zzeneg/molekula/pcbs/side36-minY/side36-right-mx-chocV2.step

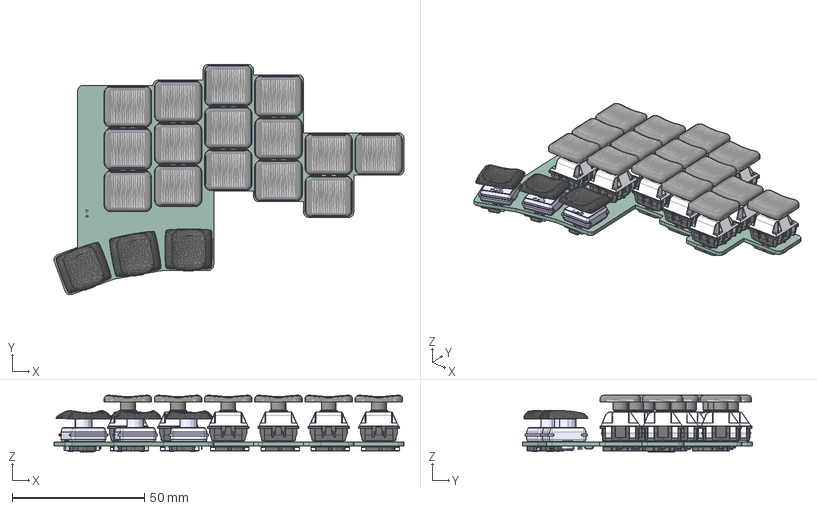
[picture p35: CAD file, 2025-01-04]
pcbs/side36-minY/side36-right-mx-chocV2.step
132.5 x 87.2 x 21.4 mm
SW_Cherry_MX_PCB_cp x 15
SW_Hotswap_Kailh_cp x 15
(Unsaved) x 15
keycap-mx-des-miny-minz-r3 v2 x 3
Kailh_PG1352 x 3
PG1350 x 3
D_SOD-123 Soldered v6 x 18
FPC-12
_autosave-pcb-right_PCB
