zzeneg/molekula/pcbs/tws-xiao-encoder/tws-xiao-encoder.step

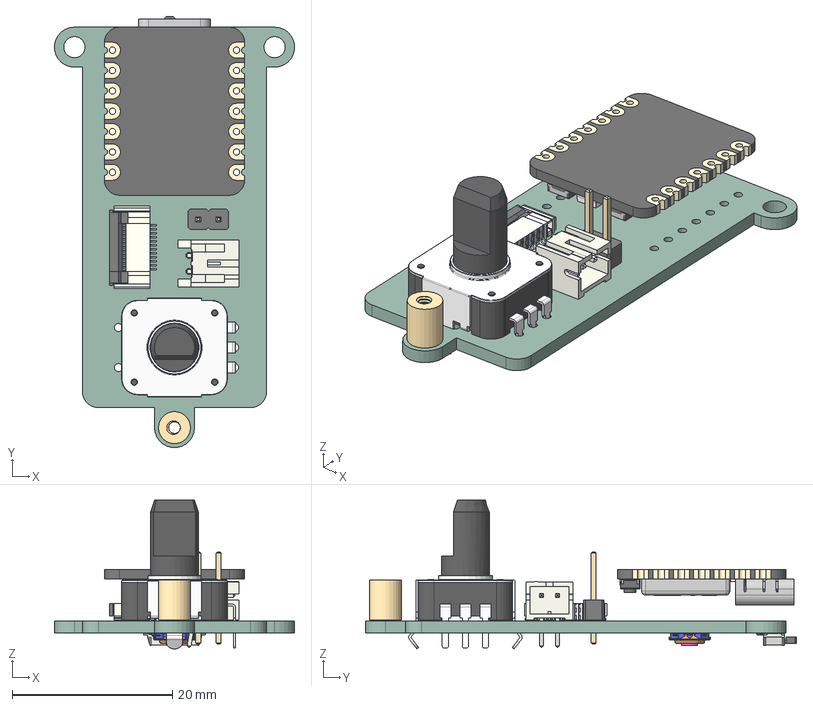
[picture p36: CAD file, 2026-09-22]
pcbs/tws-xiao-encoder/tws-xiao-encoder.step
30.0 x 53.8 x 18.6 mm
solder-nut v2
PinHeader_1x02_P254mm_Vertical
JST_S2B_PH_K
FPC-12
EC12_10mm (3)
Fusion_sp
Button_SW_SPST_SKQG_WithoutStem v1
type-c v2
smd_button v3
DOUT
DIN
VSS
VDD
smd_button v3(Mirror)
tws-xiao-encoder_PCB
