zzeneg/molekula/keyboards/Molekula2/case/bottom-right-mx cutout.dxf

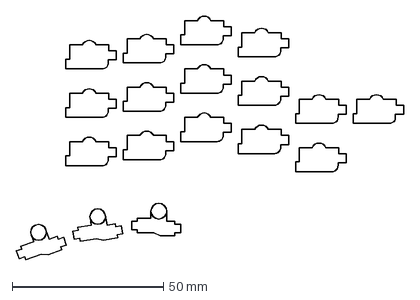
[picture p37: CAD file, 2026-05-30]
keyboards/Molekula2/case/bottom-right-mx cutout.dxf
128.1 x 80.6 mm
