zzeneg/molekula/keyboards/Molekula3/case/LP/center-nice-view.stl

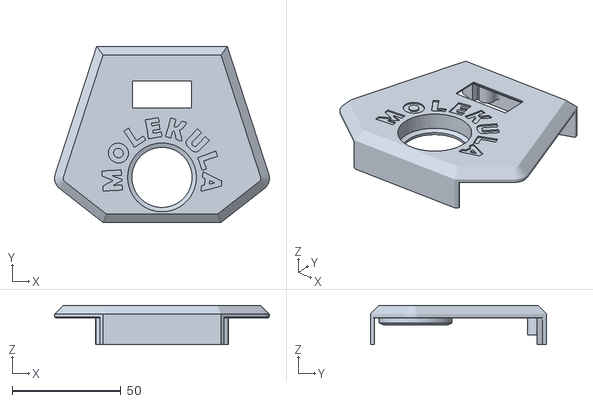
[picture p38: CAD file, 2026-05-30]
keyboards/Molekula3/case/LP/center-nice-view.stl
98.7 x 80.9 x 18.0
