zzeneg/molekula/keyboards/Molekula3/case/MX/top-left.stl

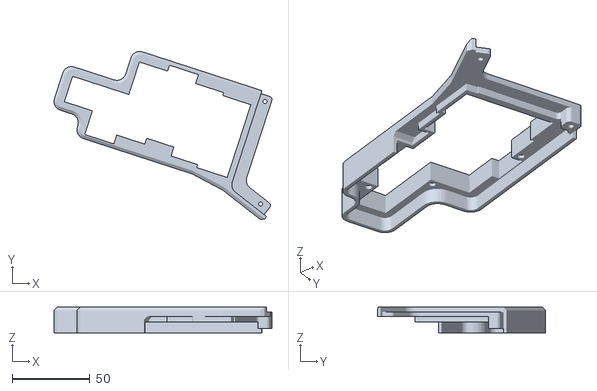
[picture p39: CAD file, 2026-05-30]
keyboards/Molekula3/case/MX/top-left.stl
140.1 x 108.1 x 16.5
