zzeneg/molekula/keyboards/MolekulaTWS/case/choc-spacing/tws.3mf

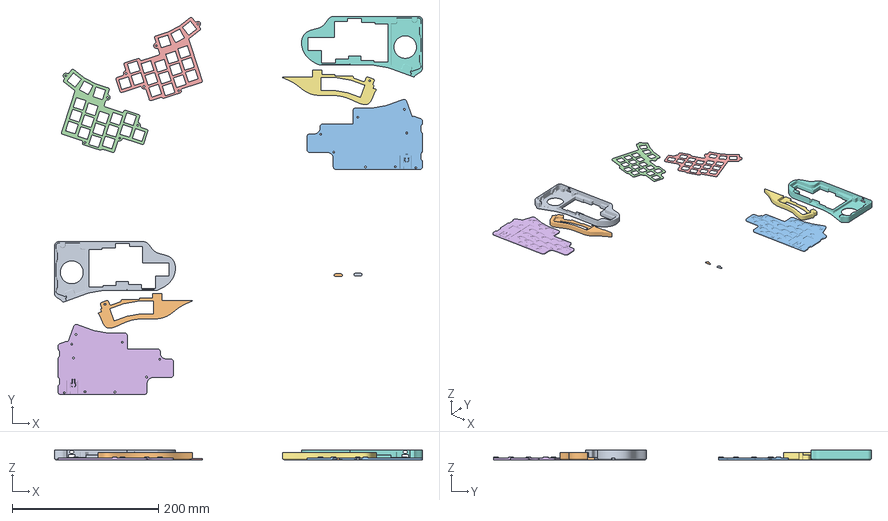
[picture p40: CAD file, 2026-09-22]
keyboards/MolekulaTWS/case/choc-spacing/tws.3mf
503.1 x 517.4 x 13.6 mm
tws-top-curved-left.stl
tws-thumb-curved-left.stl
tws-bottom-right.stl
plate-right.stl
plate-left.stl
tws-bottom-left.stl
tws-right-thumb.stl
tws-right-top.stl
tws-power-switch.stl x 2
