zzeneg/molekula/keyboards/MolekulaTWS/case/common/knob-lp.stl

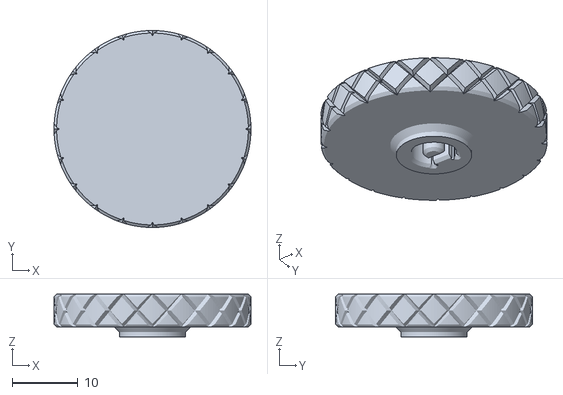
[picture p41: CAD file, 2026-09-22]
keyboards/MolekulaTWS/case/common/knob-lp.stl
30.0 x 30.0 x 6.50
