zzeneg/molekula/keycaps/MX-DES-minY/DES_r3_1.00u_x6.stl

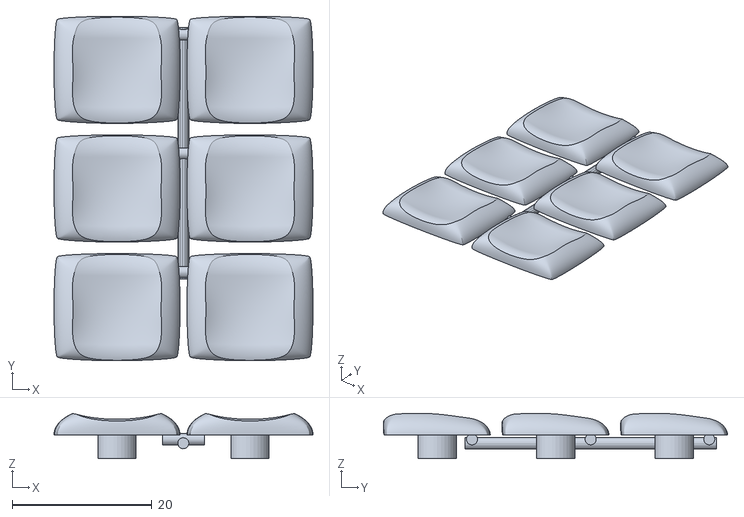
[picture p43: CAD file, 2025-01-04]
keycaps/MX-DES-minY/DES_r3_1.00u_x6.stl
37.1 x 49.4 x 6.47
