zzeneg/molekula/pcbs/central-promicro-encoder/connector-right.step

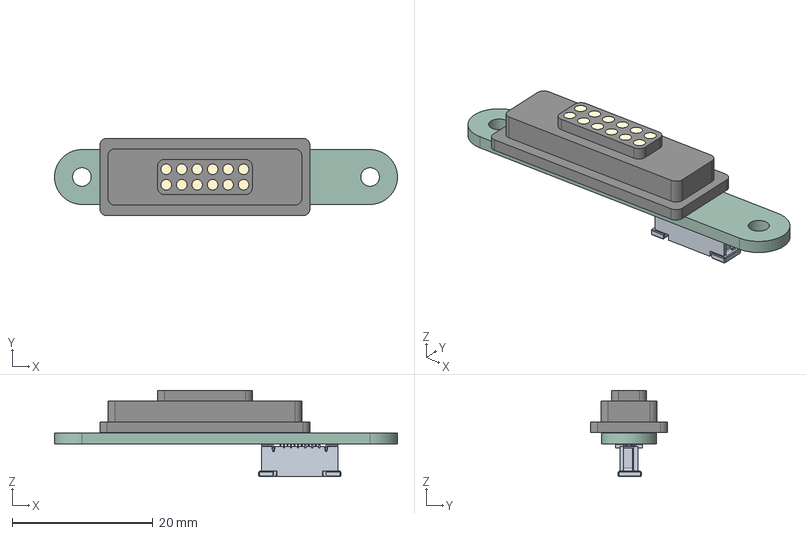
[picture p44: CAD file, 2024-11-01]
pcbs/central-promicro-encoder/connector-right.step
48.8 x 11.0 x 12.3 mm
Magnetic connector 12pin v2
C-1-1734742-2
connector-right_PCB
