zzeneg/molekula/keyboards/Molekula2/case/bottom-left-mx cutout.dxf

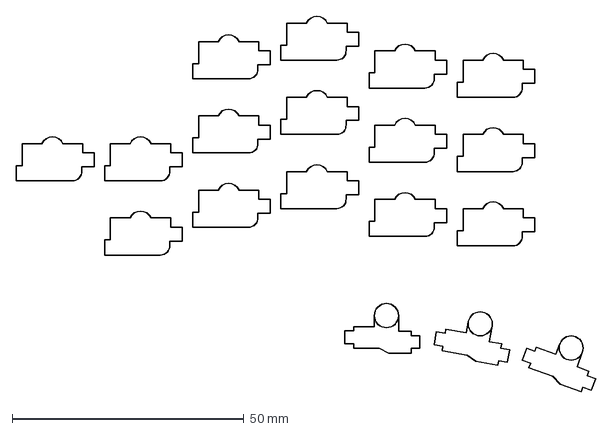
[picture p46: CAD file, 2026-05-30]
keyboards/Molekula2/case/bottom-left-mx cutout.dxf
124.8 x 80.9 mm
