zzeneg/molekula/keyboards/MolekulaTWS/case/choc-spacing/tws-bottom-left.stl

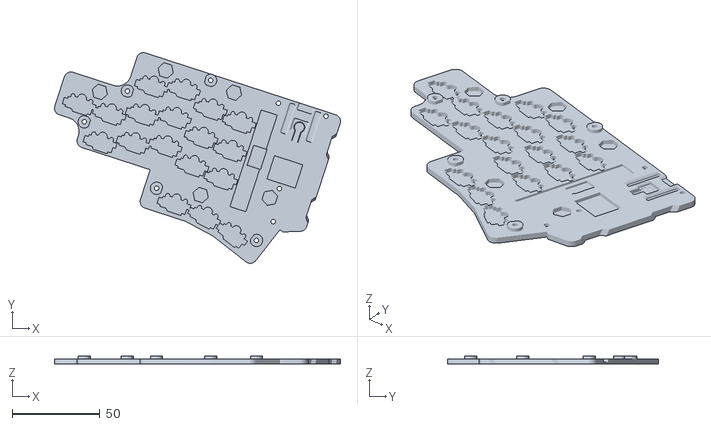
[picture p47: CAD file, 2026-09-22]
keyboards/MolekulaTWS/case/choc-spacing/tws-bottom-left.stl
163.4 x 120.3 x 4.40
