zzeneg/molekula/keyboards/MolekulaTWS/case/common/knob.stl

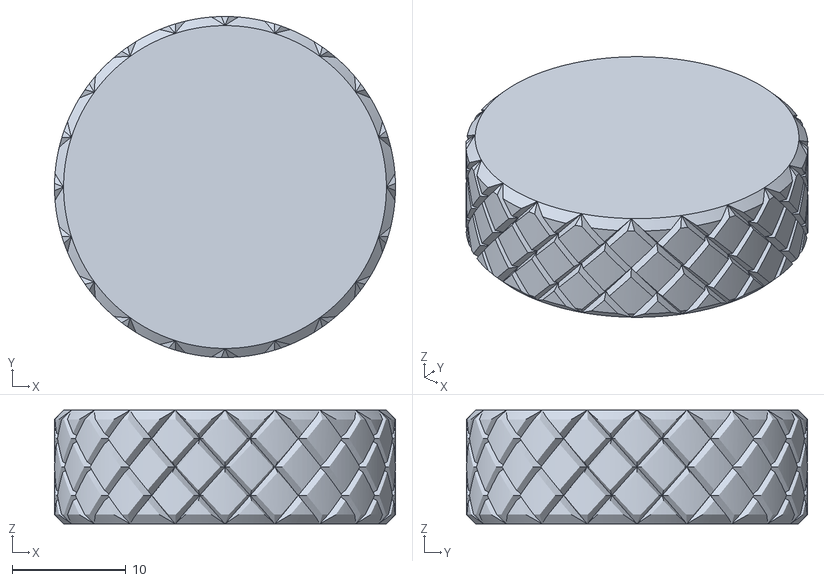
[picture p48: CAD file, 2026-06-02]
keyboards/MolekulaTWS/case/common/knob.stl
30.0 x 30.0 x 10.0
