zzeneg/molekula/keycaps/Choc-DES-minY-FDM/Choc_DES_minY-r2.stl

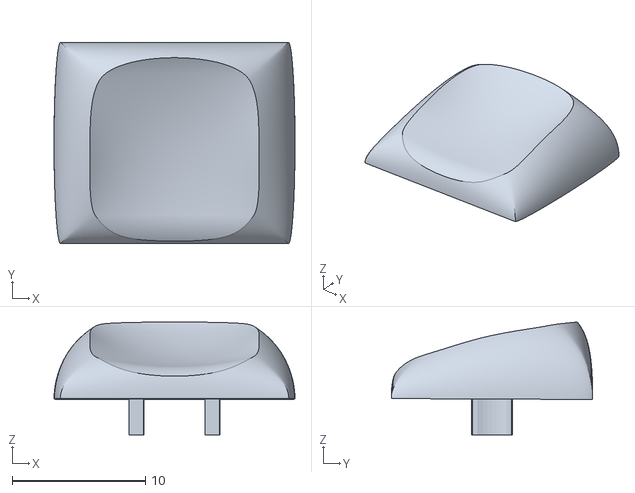
[picture p49: CAD file, 2026-05-30]
keycaps/Choc-DES-minY-FDM/Choc_DES_minY-r2.stl
18.1 x 15.1 x 8.48
