zzeneg/molekula/pcbs/central-promicro-encoder/connector-left.step

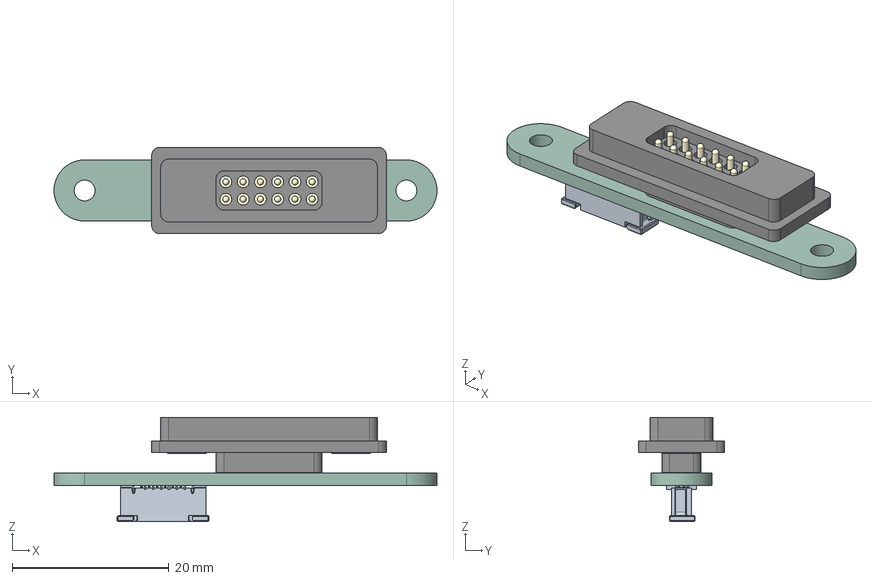
[picture p50: CAD file, 2024-11-01]
pcbs/central-promicro-encoder/connector-left.step
48.8 x 11.0 x 13.3 mm
Magnetic connector 12pin v2
C-1-1734742-2
connector-left_PCB
