zzeneg/molekula/pcbs/side36-minY/side36-right-mx-ks.step

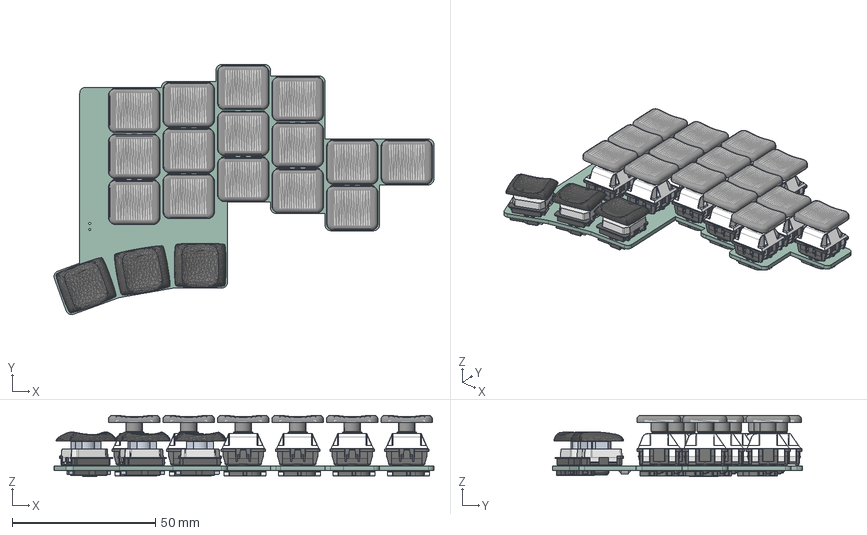
[picture p51: CAD file, 2025-01-04]
pcbs/side36-minY/side36-right-mx-ks.step
132.5 x 87.2 x 21.4 mm
SW_Cherry_MX_PCB_cp x 15
SW_Hotswap_Kailh_cp x 15
(Unsaved) x 15
CQ assembly x 6
keycap-mx-des-miny-minz-r3 v2 x 3
D_SOD-123 Soldered v6 x 18
FPC-12
pcb-right_PCB
