zzeneg/molekula/keyboards/Molekula2/case/bottom-left-choc-cutout.dxf

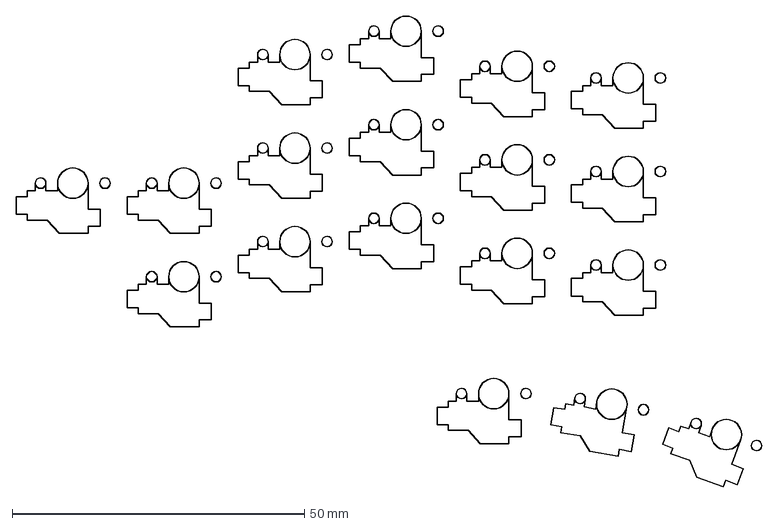
[picture p52: CAD file, 2026-05-30]
keyboards/Molekula2/case/bottom-left-choc-cutout.dxf
127.6 x 80.6 mm
