zzeneg/molekula/keyboards/Molekula3/case/common/center-bottom-logo.stl

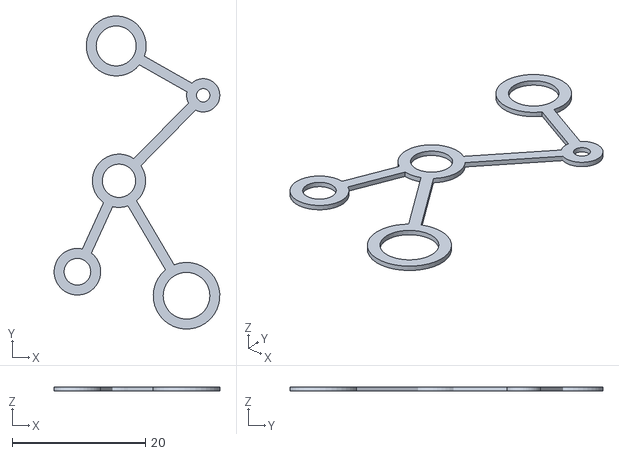
[picture p53: CAD file, 2026-05-30]
keyboards/Molekula3/case/common/center-bottom-logo.stl
24.9 x 47.0 x 0.6
