zzeneg/molekula/keycaps/Choc-DES-minY-FDM/Choc_DES_minY-r3-dot.stl

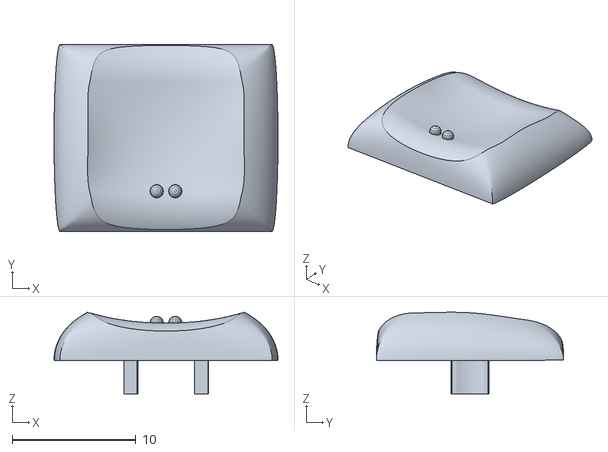
[picture p54: CAD file, 2026-05-30]
keycaps/Choc-DES-minY-FDM/Choc_DES_minY-r3-dot.stl
18.1 x 15.1 x 6.59
