zzeneg/molekula/keyboards/Molekula2/case/bottom-right-ks cutout.dxf

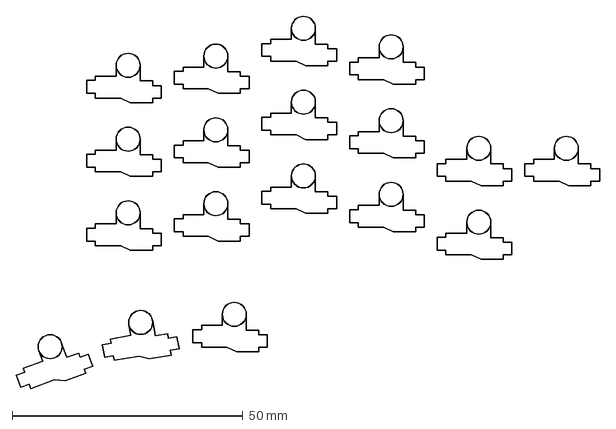
[picture p56: CAD file, 2026-05-30]
keyboards/Molekula2/case/bottom-right-ks cutout.dxf
126.4 x 80.7 mm
