zzeneg/molekula/keyboards/Molekula3/case/common/center-bottom.stl

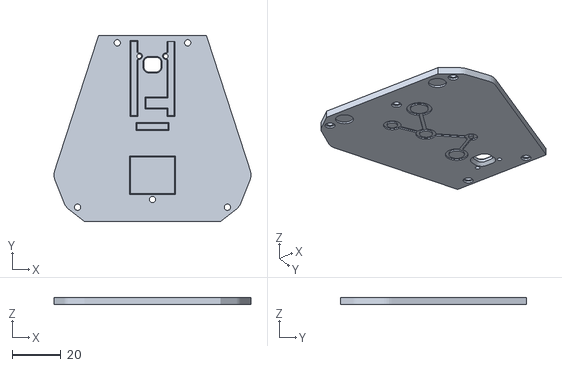
[picture p57: CAD file, 2026-05-30]
keyboards/Molekula3/case/common/center-bottom.stl
81.1 x 76.7 x 2.80
