zzeneg/molekula/keyboards/MolekulaTWS/case/choc-spacing/tws-thumb-curved-left.stl

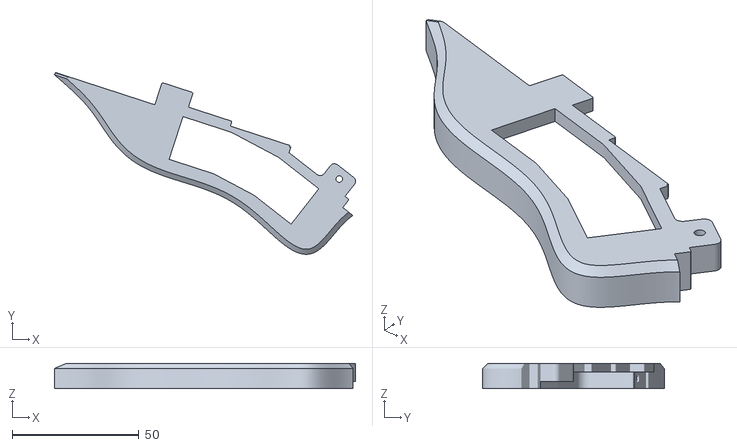
[picture p58: CAD file, 2026-09-22]
keyboards/MolekulaTWS/case/choc-spacing/tws-thumb-curved-left.stl
118.5 x 71.5 x 10.00
