zzeneg/molekula/keycaps/Choc-DES-minY-FDM/Choc_DES_minY-r2-edge-left.stl

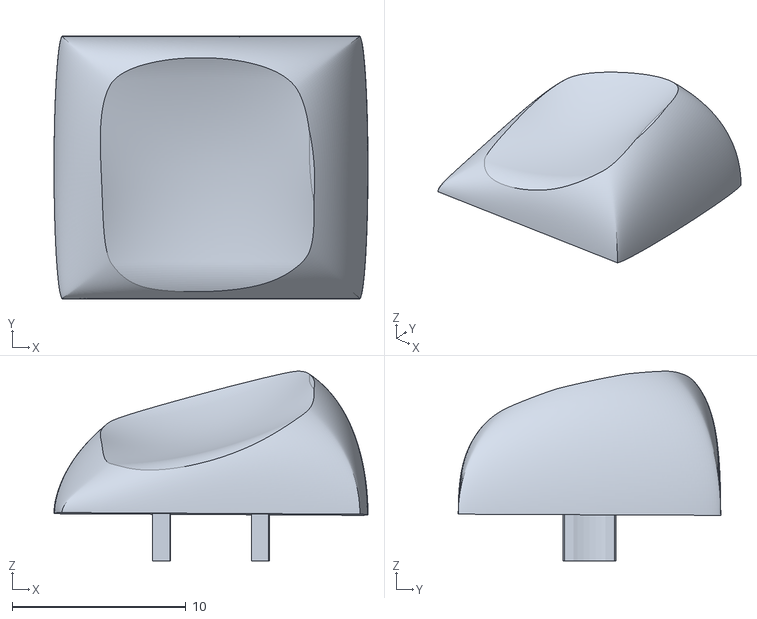
[picture p59: CAD file, 2026-05-30]
keycaps/Choc-DES-minY-FDM/Choc_DES_minY-r2-edge-left.stl
18.1 x 15.1 x 10.9
