zzeneg/molekula/pcbs/side36-minY/side36-left-chocV2.step

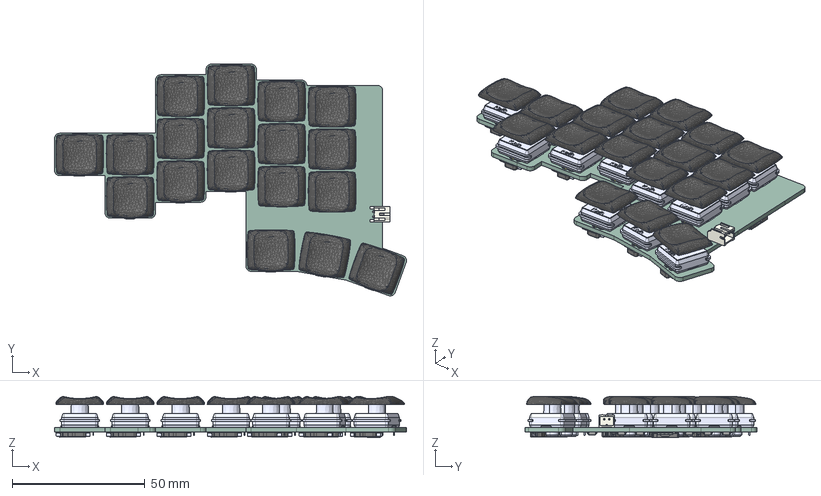
[picture p60: CAD file, 2025-01-04]
pcbs/side36-minY/side36-left-chocV2.step
132.5 x 87.2 x 15.6 mm
keycap-mx-des-miny-minz-r3 v2 x 18
Kailh_PG1352 x 18
PG1350 x 18
JST_S2B_PH_K
D_SOD-123 Soldered v6 x 18
FPC-12
pcb-left_PCB
