zzeneg/molekula/keyboards/Molekula2/case/bottom-right-choc-cutout.dxf

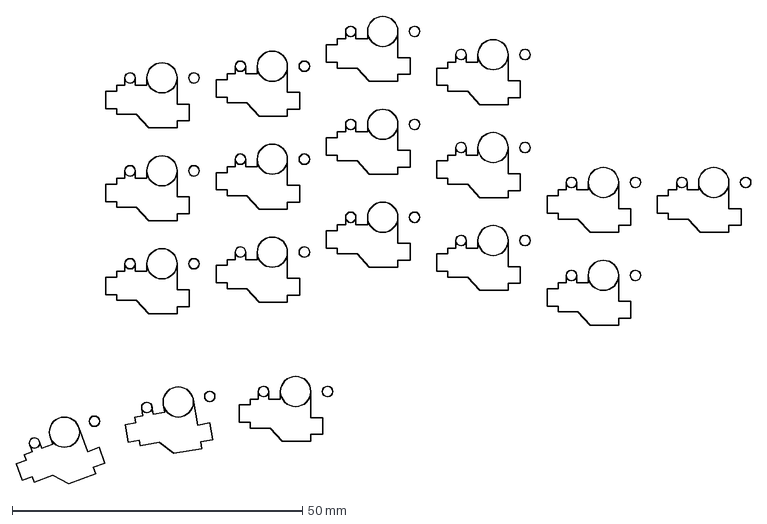
[picture p61: CAD file, 2026-05-30]
keyboards/Molekula2/case/bottom-right-choc-cutout.dxf
126.5 x 80.5 mm
