zzeneg/molekula/keyboards/Molekula3/case/common/bottom-right.stl

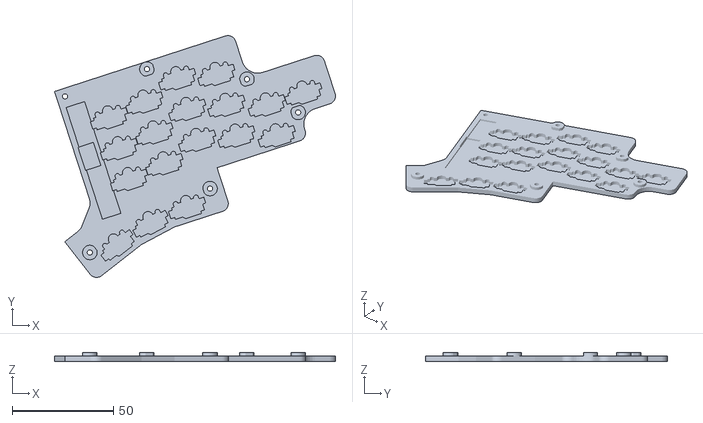
[picture p62: CAD file, 2026-05-30]
keyboards/Molekula3/case/common/bottom-right.stl
138.7 x 119.4 x 4.40
