zzeneg/molekula/keycaps/Choc-DES-minY-FDM/Choc_DES_minY-r4.stl

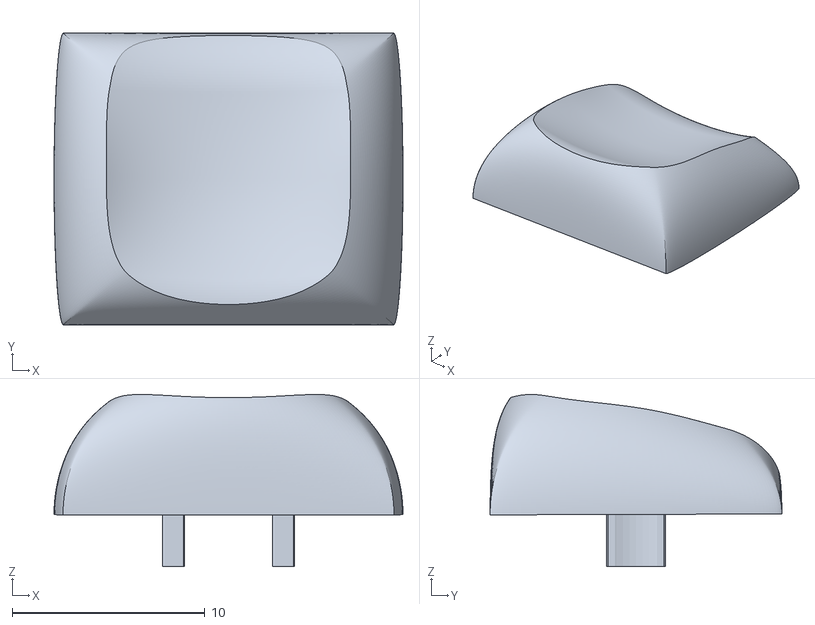
[picture p63: CAD file, 2026-05-30]
keycaps/Choc-DES-minY-FDM/Choc_DES_minY-r4.stl
18.1 x 15.1 x 8.92
