zzeneg/molekula/pcbs/side36-minY/side36-left-ks.step

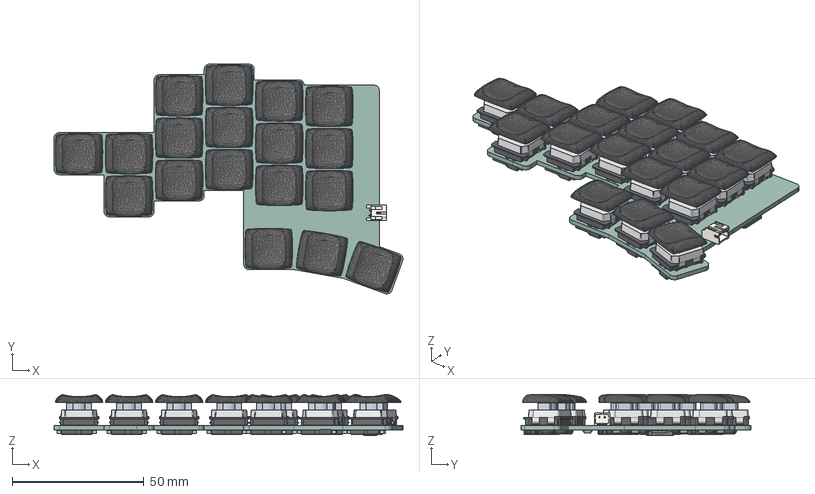
[picture p64: CAD file, 2024-11-01]
pcbs/side36-minY/side36-left-ks.step
132.5 x 87.2 x 15.6 mm
CQ assembly x 36
keycap-mx-des-miny-minz-r3 v2 x 18
JST_S2B_PH_K
D_SOD-123 Soldered v6 x 18
FPC-12
pcb-left_PCB
