zzeneg/molekula/keyboards/Molekula2/case/logo.stl

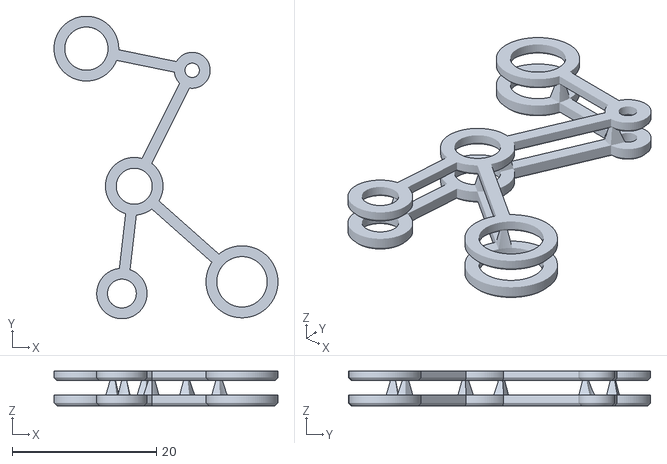
[picture p65: CAD file, 2024-12-14]
keyboards/Molekula2/case/logo.stl
31.1 x 42.0 x 4.80
