zzeneg/molekula/keyboards/Molekula3/case/common/center-text.stl

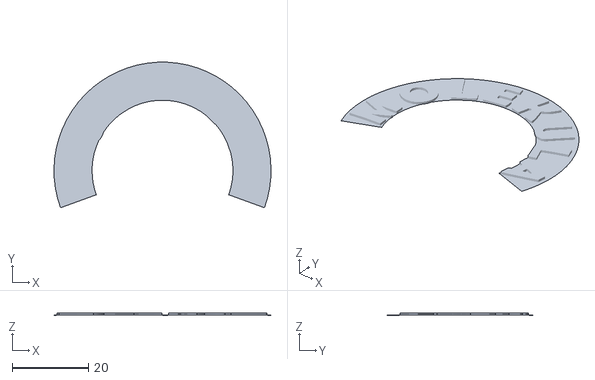
[picture p66: CAD file, 2026-05-30]
keyboards/Molekula3/case/common/center-text.stl
57.0 x 38.2 x 0.601
