zzeneg/molekula/pcbs/side36-minY/side36-right-ks.step

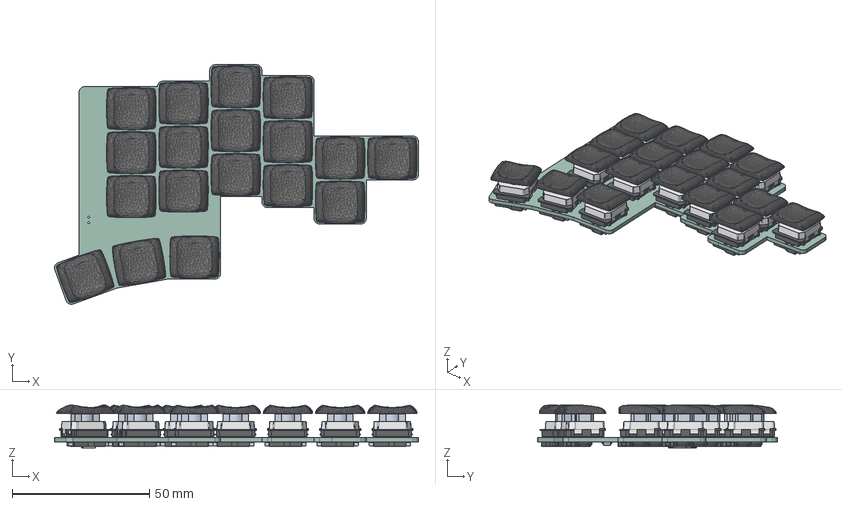
[picture p68: CAD file, 2024-11-01]
pcbs/side36-minY/side36-right-ks.step
132.5 x 87.2 x 15.6 mm
CQ assembly x 36
keycap-mx-des-miny-minz-r3 v2 x 18
D_SOD-123 Soldered v6 x 18
FPC-12
pcb-right_PCB
