zzeneg/molekula/keyboards/Molekula2/case/bottom-right-ks.stl

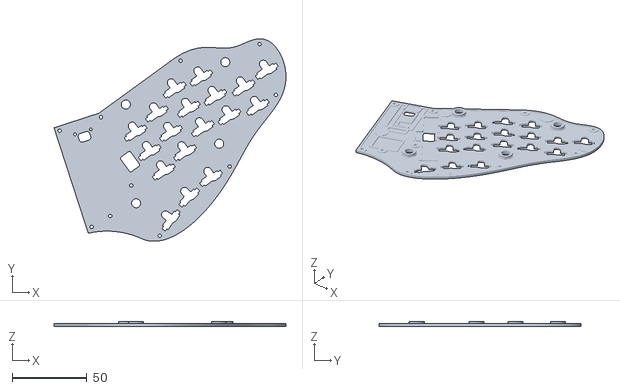
[picture p69: CAD file, 2024-12-13]
keyboards/Molekula2/case/bottom-right-ks.stl
154.7 x 135.0 x 3.60
