zzeneg/molekula/keycaps/Choc-DES-minY-FDM/Choc_DES_minY-thumb-right.stl

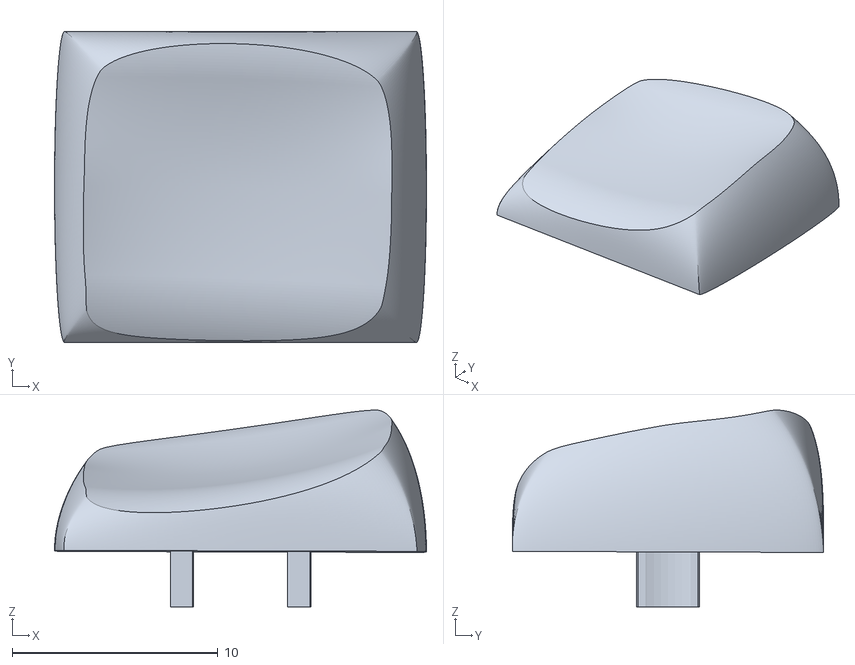
[picture p70: CAD file, 2026-05-30]
keycaps/Choc-DES-minY-FDM/Choc_DES_minY-thumb-right.stl
18.1 x 15.1 x 9.57
