zzeneg/molekula/keycaps/Choc-DES-minY-FDM/Choc_DES_minY-thumb-left.stl

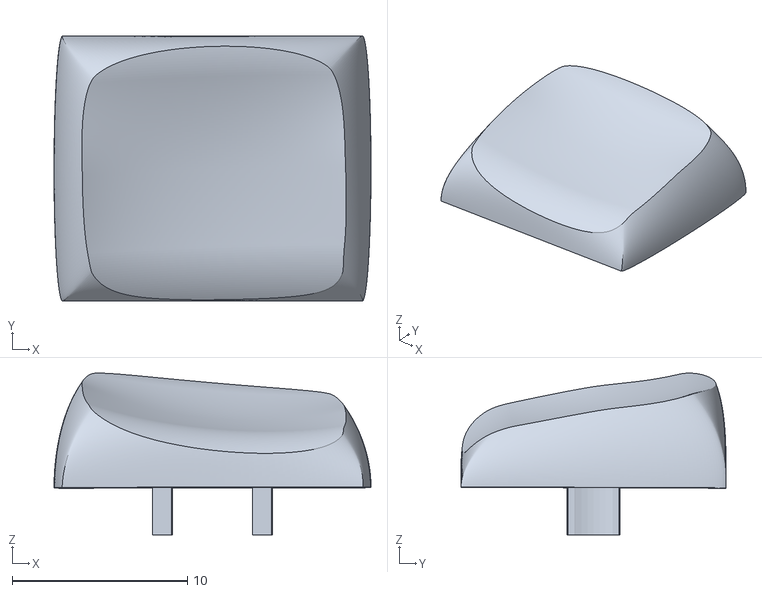
[picture p71: CAD file, 2026-05-30]
keycaps/Choc-DES-minY-FDM/Choc_DES_minY-thumb-left.stl
18.1 x 15.1 x 9.23
