zzeneg/molekula/keyboards/Molekula2/case/top-right_ks.stl

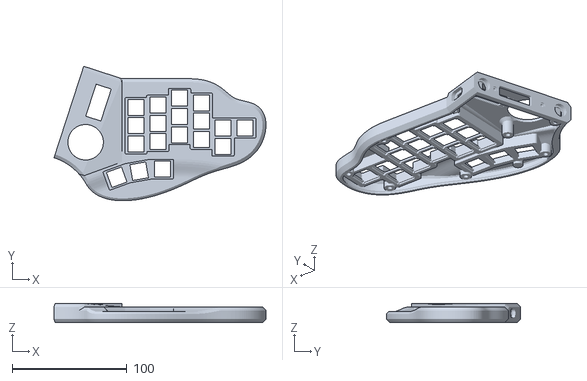
[picture p72: CAD file, 2024-12-13]
keyboards/Molekula2/case/top-right_ks.stl
185.1 x 117.4 x 16.6
