zzeneg/molekula/keyboards/Molekula2/case/bottom-left-mx.stl

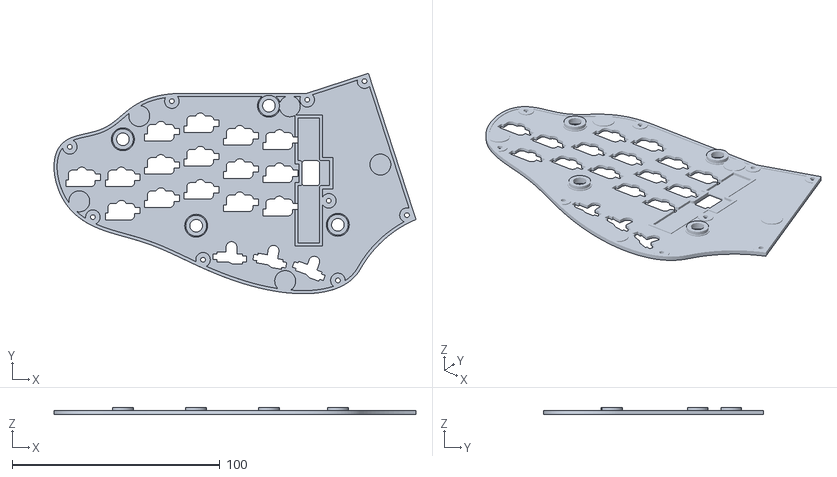
[picture p75: CAD file, 2024-12-13]
keyboards/Molekula2/case/bottom-left-mx.stl
174.2 x 106.0 x 3.60
