zzeneg/molekula/keyboards/Molekula2/case/ledview.stl

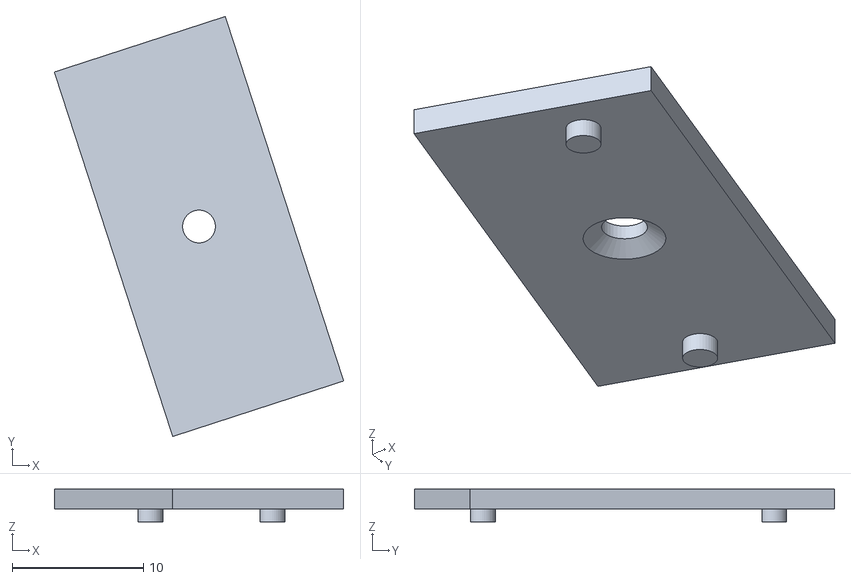
[picture p76: CAD file, 2024-12-13]
keyboards/Molekula2/case/ledview.stl
22.1 x 32.0 x 2.50
