zzeneg/molekula/keyboards/Molekula2/case/top-left-logo_chocV2.stl

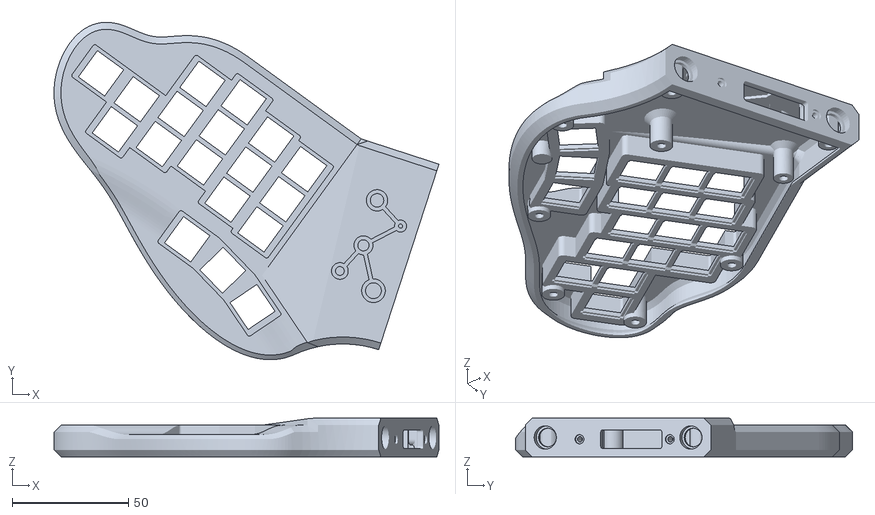
[picture p77: CAD file, 2024-11-26]
keyboards/Molekula2/case/top-left-logo_chocV2.stl
165.7 x 145.2 x 16.6
