zzeneg/molekula/keyboards/Molekula2/case/top-left_mx.stl

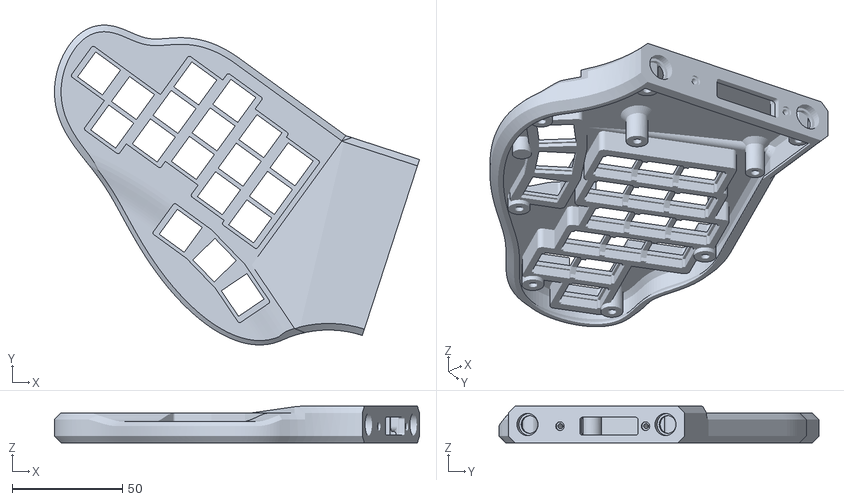
[picture p78: CAD file, 2024-11-26]
keyboards/Molekula2/case/top-left_mx.stl
165.7 x 145.2 x 16.6
